francoisgeorgy/europi-dac/software/rp2350/bootloader.py

import gc
import time
from collections import OrderedDict

import machine

import europi
from europi import (
    reset_state,
    OLED_HEIGHT,
    OLED_WIDTH,
    oled,
)
from europi_script import EuroPiScript

from utils.ui import Menu

SCRIPT_DIR = "/lib/contrib/"
REG_FILE_CODE = 0x8000
DEBUG = False


class PrintMemoryUse:
    def __init__(self, label=""):
        self.label = label

    def __enter__(self):
        gc.collect()  # Note that preemptive GC is required to get all of the scripts loaded
        if DEBUG:
            self.before = gc.mem_free()

    def __exit__(self, *args):
        if DEBUG:
            gc.collect()
            after = gc.mem_free()
            print(
                f"free: {after/1024: >6.2f}k, used: {(self.before - after)/1024: >6.2f}k   {self.label}"
            )


class BootloaderMenu(EuroPiScript):
    """A Menu which allows the user to select and execute one of the scripts available to this EuroPi. The menu will
    include the ``EuroPiScripts`` provided to it in the constructor. Button press handlers are added that allow the user
    to exit the script and return to the menu by holding both buttons down for a short period of time. If the module is
    restarted while a script is running it will boot right back into that same script.

    In the menu:

    * **Button 1:** choose the selected item
    * **Button 2:** choose the selected item
    * **Knob 1:** unused
    * **Knob 2:** change the current selection

    In a program that was launched from the menu:

    * Hold both buttons for at least 0.5s and release to return to the menu.

    :param scripts: a list of qualified class names of Classes implementing EuroPiScript to be included in the menu
    """

    def __init__(self, scripts):
        self.scripts = scripts
        self.run_request = None

    @staticmethod
    def show_progress(percentage):
        oled.hline(0, OLED_HEIGHT - 1, int(OLED_WIDTH * percentage), 1)
        oled.show()

    @staticmethod
    def get_class_for_name(script_class_name) -> type:
        try:
            module, clazz = script_class_name.rsplit(".", 1)
            return getattr(__import__(module, None, None, [None]), clazz)
        except Exception as e:
            print(
                f"Warning: Ignoring bad qualified class name: {script_class_name}\n  caused by: {e}"
            )
            return None

    @classmethod
    def load_script_classes(cls, scripts) -> "dict(str, type)":
        classes = {}
        for i, script in enumerate(scripts):
            with PrintMemoryUse(script):
                clazz = cls.get_class_for_name(script)
            if clazz:
                classes[script] = clazz
            cls.show_progress(i / len(scripts))
        return classes

    @classmethod
    def _is_europi_script(cls, c):
        return issubclass(c, EuroPiScript)

    @staticmethod
    def _build_scripts_mapping(classes):
        return OrderedDict(
            [(cls.display_name(), cls) for cls in classes if BootloaderMenu._is_europi_script(cls)]
        )

    def launch(self, selected_item):
        self.run_request = selected_item

    def exit_to_menu(self):
        self.remove_state()
        # Attempt to save the state of this script if it has been implemented.
        self.save_state()  # TODO: isn't this the wrong state?
        machine.reset()  # why doesn't machine.soft_reset() work anymore?

    def run_menu(self) -> type:
        # load menu classes
        script_classes = self.load_script_classes(self.scripts)
        scripts_mapping = BootloaderMenu._build_scripts_mapping(script_classes.values())
        self.menu = Menu(
            items=list(sorted(scripts_mapping.keys())),
            select_func=self.launch,
            select_knob=europi.k2,
            choice_buttons=[europi.b1, europi.b2],
        )

        # let the user make a selection
        old_selected = -1
        while not self.run_request:
            if old_selected != self.menu.selected:
                old_selected = self.menu.selected
                self.menu.draw_menu()
            time.sleep(0.1)
        return scripts_mapping[self.run_request]

    def main(self):
        script_class_name = self.load_state_str()
        script_class = None

        if script_class_name:
            script_class = self.get_class_for_name(script_class_name)

        if not script_class:
            script_class = self.run_menu()
            self.save_state_str(f"{script_class.__module__}.{script_class.__name__}")
            machine.reset()
        else:
            # setup the exit handlers, and execute the selection
            europi.b1._handler_both(europi.b2, self.exit_to_menu)
            europi.b2._handler_both(europi.b1, self.exit_to_menu)

            script_class().main()
