francoisgeorgy/europi-dac/software/rp2350/default_calibration.py

INPUT_CALIBRATION_VALUES = [0, 4608, 9216, 13935, 18560, 23296, 28032, 32768, 37504, 42368, 47184, 51968]

OUTPUT_CALIBRATION_VALUES = [
    0,  # 0V
    6300,  # 1V
    12575,  # 2V
    19150,  # 3V
    25375,  # 4V
    31625,  # 5V
    38150,  # 6V
    44225,  # 7V
    50525,  # 8V
    56950,  # 9V
    63475,  # 10V
]
OUTPUT_DAC_CALIBRATION_VALUES = [[
    0,  # 0V
    388,  # 1V
    776,  # 2V
    1164,  # 3V
    1552,  # 4V
    1939,  # 5V
    2327,  # 6V
    2715,  # 7V
    3103,  # 8V
    3491,  # 9V
    3879  # 10V
], [
    0,  # 0V
    388,  # 1V
    776,  # 2V
    1164,  # 3V
    1552,  # 4V
    1939,  # 5V
    2327,  # 6V
    2715,  # 7V
    3103,  # 8V
    3491,  # 9V
    3879  # 10V
], [
    0,  # 0V
    388,  # 1V
    776,  # 2V
    1164,  # 3V
    1552,  # 4V
    1939,  # 5V
    2327,  # 6V
    2715,  # 7V
    3103,  # 8V
    3491,  # 9V
    3879  # 10V
], [
    0,  # 0V
    388,  # 1V
    776,  # 2V
    1164,  # 3V
    1552,  # 4V
    1939,  # 5V
    2327,  # 6V
    2715,  # 7V
    3103,  # 8V
    3491,  # 9V
    3879  # 10V
]
]
